pludov/indi_allinone/ucontroler/BinSerialWriteBuffer.h

#ifndef BINSERIALWRITEBUFFER_H_
#define BINSERIALWRITEBUFFER_H_ 1

#include "WriteBuffer.h"

class BinSerialReadBuffer;

class BinSerialWriteBuffer : public WriteBuffer {
	friend class BinSerialReadBuffer;
    void appendSymbol(const Symbol & s);
public:
    void appendPacketControl(uint8_t v);
    void appendUid(uint8_t uid);

    void appendUint7(uint8_t value) { WriteBuffer::append(value); }
    void writeStringChar(uint8_t ch);

public:
	BinSerialWriteBuffer(uint8_t * into, int size);
	virtual ~BinSerialWriteBuffer();

	void debug() const;

    virtual bool finish();
    
	virtual bool supportUpdateValue() const;

	virtual void startWelcomePacket();

	virtual void writeDeleteVectorPacket(const IndiVector & vec);
	
	virtual void startAnnounceVectorPacket(const IndiVector & vec);
	virtual void endAnnounceVectorPacket(const IndiVector & vec);
	
	virtual void startMutateVectorPacket(const IndiVector & vec);
	virtual void endMutateVectorPacket(const IndiVector & vec);

	virtual void writeVectorFlag(uint8_t flag);

	// during announce/mutate
	virtual void startMember(const IndiVector & vec);
	virtual void endMember(const IndiVector & vec);

	virtual void startUpdateValuesPacket(const IndiVector & vec);
	virtual void endUpdateValuesPacket(const IndiVector & vec);

	virtual void writeVectorGroup(const Symbol & group);
	virtual void writeVectorName(const Symbol & name);
	virtual void writeVectorLabel(const Symbol & name);
	virtual void writeVectorUid(uint8_t uid);
	virtual void writeVectorMemberSubtype(uint8_t subtype);
	virtual void writeVectorMemberName(const Symbol & name);
	virtual void writeVectorMemberLabel(const Symbol & name);
	virtual void writeFloat(float value);
	virtual void writeInt(int32_t value);
	virtual void writeString(const char * c, int maxSize);
	virtual void writeBool(bool b);
};


#endif
