pludov/indi_allinone/ucontroler/IndiVectorMemberStorage.cpp

/*
 * IndiVectorStorage.cpp
 *
 *  Created on: 9 déc. 2017
 *      Author: ludovic
 */
#ifdef ARDUINO
#include <Arduino.h>
#endif

#include "IndiVectorMemberStorage.h"

IndiVectorMemberStorage::IndiVectorMemberStorage() {

}

IndiVectorMemberStorage::~IndiVectorMemberStorage() {
}
