pludov/indi_allinone/ucontroler/Scheduled.cpp

/*
 * Scheduled.cpp
 *
 *  Created on: 3 févr. 2015
 *      Author: utilisateur
 */

#include <Arduino.h>
#include "Scheduled.h"
#include "Scheduler.h"

Scheduled::Scheduled(const Symbol & debug)
	: debugName(debug)
{
	this->debugName = debug;
	this->nextTick = UTime::never();
	this->priority = 0;
	this->tickExpectedDuration = US(0);
	this->nextScheduled = Scheduler::instance().first;
	Scheduler::instance().first = this;
}

Scheduled::~Scheduled()
{
	// FIXME: remove from scheduler not implemented
}
